AndreasArendt/gpsdo/software/gpsdo/src/filter/filter.h

/*
 * filter.h
 *
 *  Created on: Nov 7, 2025
 *      Author: andia
 */

#ifndef FILTER_FILTER_H_
#define FILTER_FILTER_H_

#include <stdint.h>
#include "flatbuf_defs.h"

void filter_init(void);
void filter_predict(float voltage_ctrl);
void filter_correct(float raw_count);

void filter_step(float raw_count, float voltage_ctrl);

bool filter_pre_check(float delta);
float filter_ema(float x, float prev_y, float alpha);

float filter_get_phase_count();
float filter_get_frequency_offset_Hz();
float filter_get_frequency_drift_HzDs();
void filter_get_kf_debug_flatbuf(KF_DebugSnapshot *dst);

#endif /* FILTER_FILTER_H_ */
