AndreasArendt/gpsdo/software/gpsdo/src/Tasks/manager/manager.c

/*
 * manager.c
 *
 *  Created on: Oct 25, 2025
 *      Author: andia
 */

#include "manager.h"
#include "hal.h"
#include "flatbuf_message_builder.h"
#include "pps.h"

#include <math.h>

#define ADC_VREF 3.3f
#define ADC_MAX_VALUE 4096.0f

static float voltage__V = 0.0f;
static float temperature__C = 0.0f;

float get_volt_meas() {
	return voltage__V;
}

float get_temperature() {
	return temperature__C;
}

// taken from: https://viereck.ch/ntc/
float ntc_calc_temperature(uint16_t adc_value) {

	float r = 10e3;
	float ntcR25 = 10e3;
	float ntcBeta = 3425;

	float measuredVoltage = adc_value / ADC_MAX_VALUE * ADC_VREF;
	float rNtc = measuredVoltage * r / (ADC_VREF - measuredVoltage);
	float temperature__C = 1
			/ (logf(rNtc / ntcR25) / ntcBeta + 1 / (273.15 + 25)) - 273.15;

	return temperature__C;
}

// calculate control voltage for oscillator
float vref_ocxo_calc(uint16_t adc_value) {
	return (adc_value / ADC_MAX_VALUE) * ADC_VREF;
}

void mangerTask(void *argument) {
	pps_init();

	hal_initialized = 1;

	for (;;) {
		uint16_t ch1 = adc_dma_buffer[0];
		uint16_t ch3 = adc_dma_buffer[1];

		voltage__V = vref_ocxo_calc(ch1);
		temperature__C = ntc_calc_temperature(ch3);

		osDelay(1000);
	}
}
