AndreasArendt/gpsdo/software/gpsdo/src/Tasks/manager/manager.h

/*
 * manager.h
 *
 *  Created on: Oct 25, 2025
 *      Author: andia
 */

#ifndef TASKS_MANAGER_MANAGER_H_
#define TASKS_MANAGER_MANAGER_H_

float get_volt_meas();
float get_temperature();

#endif /* TASKS_MANAGER_MANAGER_H_ */
