AndreasArendt/gpsdo/software/gpsdo/src/led/led.h

/*
 * led.h
 *
 *  Created on: Oct 28, 2025
 *      Author: andia
 */

#ifndef LED_LED_H_
#define LED_LED_H_

void toggle_led_red();
void set_led_red();
void reset_led_red();

void toggle_led_orange();
void set_led_orange();
void reset_led_orange();


#endif
