AndreasArendt/gpsdo/software/gpsdo/src/Tasks/com_usb/flatbuf_flatcc_alloc.h

/*
 * flatbuf_flatcc_alloc.h
 *
 *  Created on: Nov 23, 2025
 *      Author: andia
 */

#ifndef TASKS_COM_USB_FLATBUF_FLATCC_ALLOC_H_
#define TASKS_COM_USB_FLATBUF_FLATCC_ALLOC_H_

void flatbuf_select_status_arena(void);
void flatbuf_select_kf_arena(void);

#endif /* TASKS_COM_USB_FLATBUF_FLATCC_ALLOC_H_ */
