AndreasArendt/gpsdo/software/gpsdo/src/hal.h

/*
 * hal.h
 *
 *  Created on: Oct 18, 2025
 *      Author: andia
 */

#ifndef HAL_H_
#define HAL_H_

#include "cmsis_os.h"
#include "stm32f4xx_hal.h"
#include "message_buffer.h"
#include "usbd_def.h"
#include "queue.h"

extern uint16_t adc_dma_buffer[2];  // CH1, CH3 [voltage, temperature]
extern uint8_t hal_initialized;

extern TIM_HandleTypeDef htim1;
extern TIM_HandleTypeDef htim2;
extern TIM_HandleTypeDef htim5;

extern ADC_HandleTypeDef hadc1;

extern USBD_HandleTypeDef hUsbDeviceFS;

extern SPI_HandleTypeDef hspi1;

extern osSemaphoreId_t xPPSSemaphoreHandle;

#endif /* HAL_H_ */
